Harshul-Tripathi/asset-tracking-system/firmware/stm32-anchor-hub/nucleo-u575zi-q_bu03/Core/Src/platform/deca_spi.c

/*! ----------------------------------------------------------------------------
 * @file    deca_spi.c
 * @brief   SPI access functions
 *
 * @attention
 *
 * Copyright 2015 - 2021 (c) DecaWave Ltd, Dublin, Ireland.
 *
 * All rights reserved.
 *
 * @author DecaWave
 */

#include <deca_device_api.h>
#include <deca_spi.h>
#include <port.h>
#include <stm32u5xx_hal_def.h>
#include <string.h>


extern SPI_HandleTypeDef    *hcurrent_active_spi;/*clocked from 72MHz*/
extern uint16_t             pin_io_active_spi;
extern GPIO_PinState        SPI_CS_state;

/****************************************************************************
 *
 *
 *                              DWxxx SPI section
 *
 *******************************************************************************/
/*! ------------------------------------------------------------------------------------------------------------------
 * Function: openspi()
 *
 * Low level abstract function to open and initialise access to the SPI device.
 * returns 0 for success, or -1 for error
 */
int openspi(/*SPI_TypeDef* SPIx*/)
{
    return 0;
} // end openspi()

/*! ------------------------------------------------------------------------------------------------------------------
 * Function: closespi()
 *
 * Low level abstract function to close the the SPI device.
 * returns 0 for success, or -1 for error
 */
int closespi(void)
{
    return 0;
} // end closespi()

/*! ------------------------------------------------------------------------------------------------------------------
 * Function: writetospiwithcrc()
 *
 * Low level abstract function to write to the SPI when SPI CRC mode is used
 * Takes two separate byte buffers for write header and write data, and a CRC8 byte which is written last
 * returns 0 for success, or -1 for error
 */
int32_t writetospiwithcrc(uint16_t headerLength, const uint8_t *headerBuffer, uint16_t bodyLength, const uint8_t *bodyBuffer, uint8_t crc8)
{
#ifdef DWT_ENABLE_CRC
    decaIrqStatus_t stat;
    stat = decamutexon();
    while (HAL_SPI_GetState(hcurrent_active_spi) != HAL_SPI_STATE_READY);

    HAL_GPIO_WritePin(UWB_CS_GPIO_Port, pin_io_active_spi, SPI_CS_state); /**< Put chip select line low */


    HAL_SPI_Transmit(hcurrent_active_spi, (uint8_t *)headerBuffer, headerLength, 10);    /* Send header in polling mode */
    HAL_SPI_Transmit(hcurrent_active_spi, (uint8_t *)bodyBuffer, bodyLength, 10);        /* Send data in polling mode */
    HAL_SPI_Transmit(hcurrent_active_spi, (uint8_t *)&crc8, 1, 10);      /* Send data in polling mode */

    HAL_GPIO_WritePin(UWB_CS_GPIO_Port, pin_io_active_spi,(GPIO_PinState)(!((uint8_t)SPI_CS_state))); /**< Put chip select line high */

    decamutexoff(stat);
#endif //DWT_ENABLE_CRC
    return 0;
} // end writetospiwithcrc()

/*! ------------------------------------------------------------------------------------------------------------------
 * Function: writetospi()
 *
 * Low level abstract function to write to the SPI
 * Takes two separate byte buffers for write header and write data
 * returns 0 for success, or -1 for error
 */
int32_t writetospi(uint16_t headerLength, const uint8_t *headerBuffer, uint16_t bodyLength, const uint8_t *bodyBuffer)
{
    decaIrqStatus_t stat;
    stat = decamutexon();

    while (HAL_SPI_GetState(hcurrent_active_spi) != HAL_SPI_STATE_READY);

    HAL_GPIO_WritePin(UWB_CS_GPIO_Port, pin_io_active_spi, SPI_CS_state); /**< Put chip select line low */

    HAL_SPI_Transmit(hcurrent_active_spi, (uint8_t *)headerBuffer, headerLength, HAL_MAX_DELAY); /* Send header in polling mode */

    if(bodyLength != 0)
    {
        HAL_SPI_Transmit(hcurrent_active_spi, (uint8_t *)bodyBuffer,   bodyLength, HAL_MAX_DELAY);     /* Send data in polling mode */
    }

    HAL_GPIO_WritePin(UWB_CS_GPIO_Port, pin_io_active_spi, (GPIO_PinState)(!((uint8_t)SPI_CS_state))); /**< Put chip select line high */

    decamutexoff(stat);

    return 0;
} // end writetospi()

/*! ------------------------------------------------------------------------------------------------------------------
 * @fn spi_cs_low_delay()
 *
 * @brief This function sets the CS to '0' for ms delay and than raises it up
 *
 * input parameters:
 * @param ms_delay - The delay for CS to be in '0' state
 *
 * no return value
 */
uint16_t spi_cs_low_delay(uint16_t delay_ms)
{
    /* Blocking: Check whether previous transfer has been finished */
    while (HAL_SPI_GetState(hcurrent_active_spi) != HAL_SPI_STATE_READY);
    /* Process Locked */
    __HAL_LOCK(hcurrent_active_spi);
    HAL_GPIO_WritePin(UWB_CS_GPIO_Port, pin_io_active_spi, SPI_CS_state); /**< Put chip select line low */
    Sleep(delay_ms);
    HAL_GPIO_WritePin(UWB_CS_GPIO_Port, pin_io_active_spi, (GPIO_PinState)(!((uint8_t)SPI_CS_state))); /**< Put chip select line high */
    /* Process Unlocked */
    __HAL_UNLOCK(hcurrent_active_spi);

    return 0;
}

/*! ------------------------------------------------------------------------------------------------------------------
 * Function: readfromspi()
 *
 * Low level abstract function to read from the SPI
 * Takes two separate byte buffers for write header and read data
 * returns the offset into read buffer where first byte of read data may be found,
 * or returns -1 if there was an error
 */
//#pragma GCC optimize ("O3")
int32_t readfromspi(uint16_t headerLength, uint8_t *headerBuffer, uint16_t readlength, uint8_t *readBuffer)
{

    decaIrqStatus_t stat;
    stat = decamutexon();

    /* Blocking: Check whether previous transfer has been finished */
    while (HAL_SPI_GetState(hcurrent_active_spi) != HAL_SPI_STATE_READY);

    HAL_GPIO_WritePin(UWB_CS_GPIO_Port, pin_io_active_spi, SPI_CS_state); /**< Put chip select line low */

    uint8_t tx_buf[128] = {0};
    uint8_t rx_buf[128] = {0};
    uint16_t total_len = headerLength + readlength;

    if (total_len <= 128) {
        memcpy(tx_buf, headerBuffer, headerLength);
        HAL_SPI_TransmitReceive(hcurrent_active_spi, tx_buf, rx_buf, total_len, HAL_MAX_DELAY);
        memcpy(readBuffer, &rx_buf[headerLength], readlength);
    } else {
        /* Fallback for long reads (if any) */
        HAL_SPI_Transmit(hcurrent_active_spi, (uint8_t*)headerBuffer, headerLength, HAL_MAX_DELAY);
        HAL_SPI_Receive(hcurrent_active_spi, readBuffer, readlength, HAL_MAX_DELAY);
    }

    HAL_GPIO_WritePin(UWB_CS_GPIO_Port, pin_io_active_spi, (GPIO_PinState)(!((uint8_t)SPI_CS_state))); /**< Put chip select line high */

    decamutexoff(stat);

    return 0;
} // end readfromspi()

/****************************************************************************
 *
 *                              END OF DW3xxx SPI section
 *
 *******************************************************************************/
